TingliangZhang/HandGestureCamera/宣传素材/屏幕截图 2022-03-20 224517.png

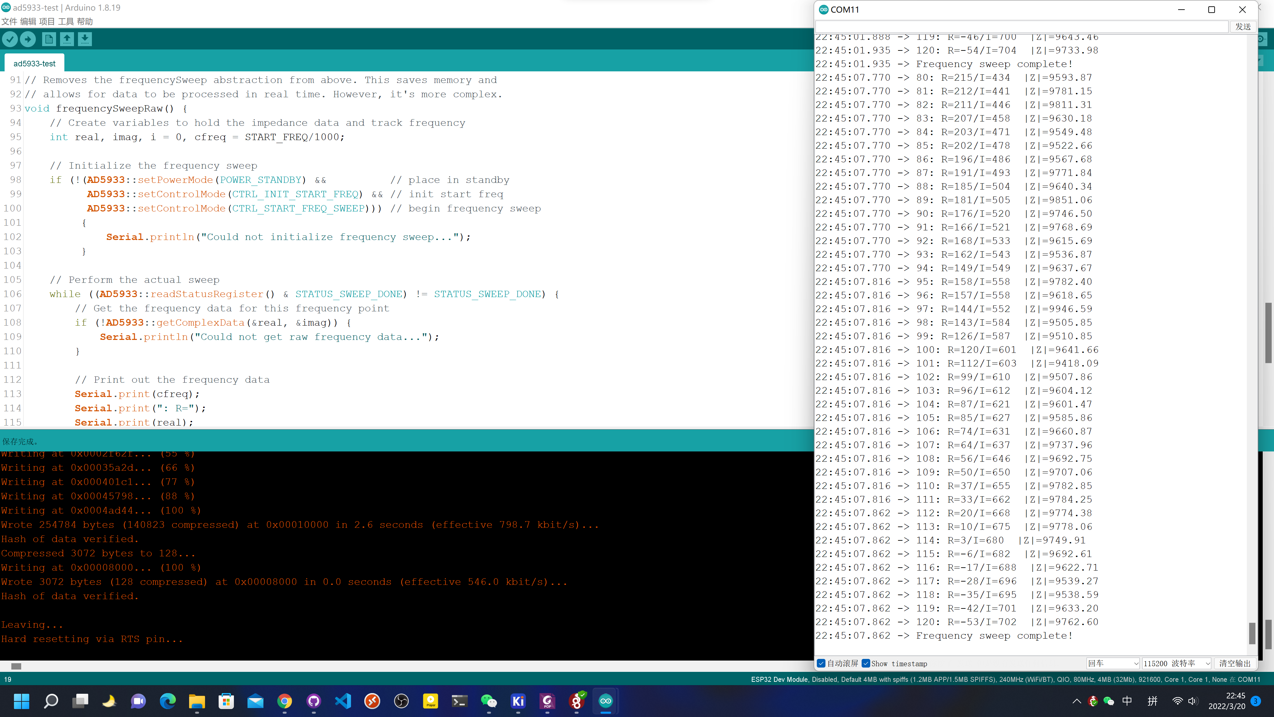
宣传素材/屏幕截图 2022-03-20 224517.png
