TingliangZhang/HandGestureCamera/宣传素材/屏幕截图 2022-04-06 172704.png

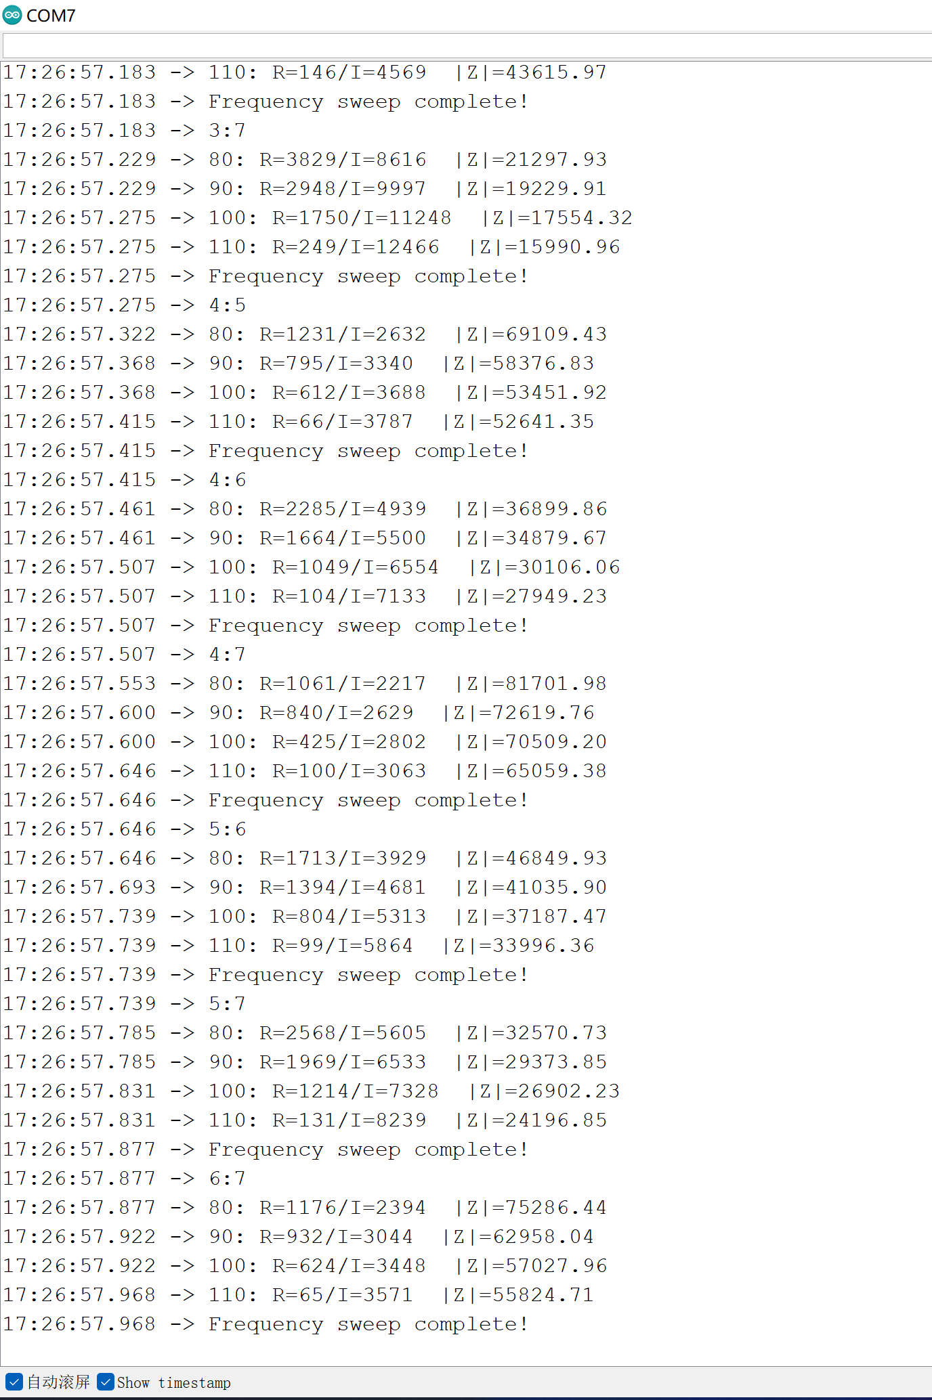
宣传素材/屏幕截图 2022-04-06 172704.png
